African-Robotics-Unit/boom-shunt-regulator/ReworkSchematic/BoomShuntRegulator.kicad_pcb

## KiCad design schematics/iec_interface.kicad_sch

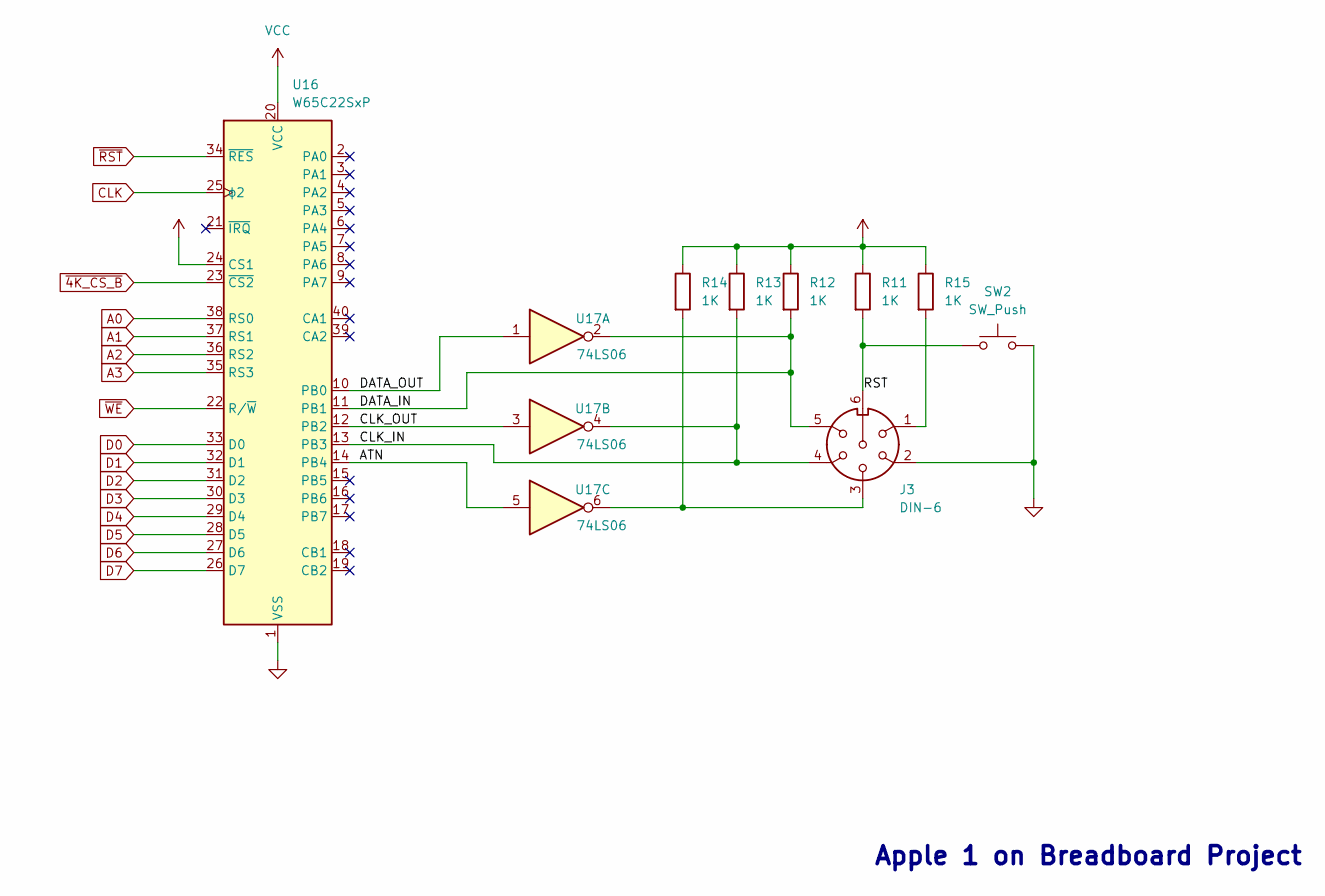
[picture p4: schematic iec_interface.kicad_sch]

Parts:
J3: DIN-6
R11, R12, R13, R14, R15: 1K
SW2: SW_Push
U16: W65C22SxP; DIP-40_W15.24mm
U17: 74LS06

Connections:
A0: U16.38 (RS0)
A1: U16.37 (RS1)
A2: U16.36 (RS2)
A3: U16.35 (RS3)
ATN: U16.14 (PB4), U17.5
CLK: U16.25 (ϕ2)
CLK_IN: J3.4, R13.2, U16.13 (PB3), U17.4
CLK_OUT: U16.12 (PB2), U17.3
D0: U16.33 (D0)
D1: U16.32 (D1)
D2: U16.31 (D2)
D3: U16.30 (D3)
D4: U16.29 (D4)
D5: U16.28 (D5)
D6: U16.27 (D6)
D7: U16.26 (D7)
DATA_IN: J3.5, R12.2, U16.11 (PB1), U17.2
DATA_OUT: U16.10 (PB0), U17.1
GND: J3.2, SW2.2, U16.1 (VSS)
unnamed: J3.1, R15.2
unnamed: J3.3, R14.2, U17.6
RST: J3.6, R11.2, SW2.1
VCC: R11.1, R12.1, R13.1, R14.1, R15.1, U16.20 (VCC), U16.24 (CS1)
~4K_CS_B: U16.23 (~CS2)
~RST: U16.34 (~RES)
~WE: U16.22 (R/~W)

Notes on the sheet:
Apple 1 on Breadboard Project
